akashlevy/ember-pcb/ember-pcb.kicad_sch

## KiCad design ember-pcb.kicad_sch (2023-03-14)

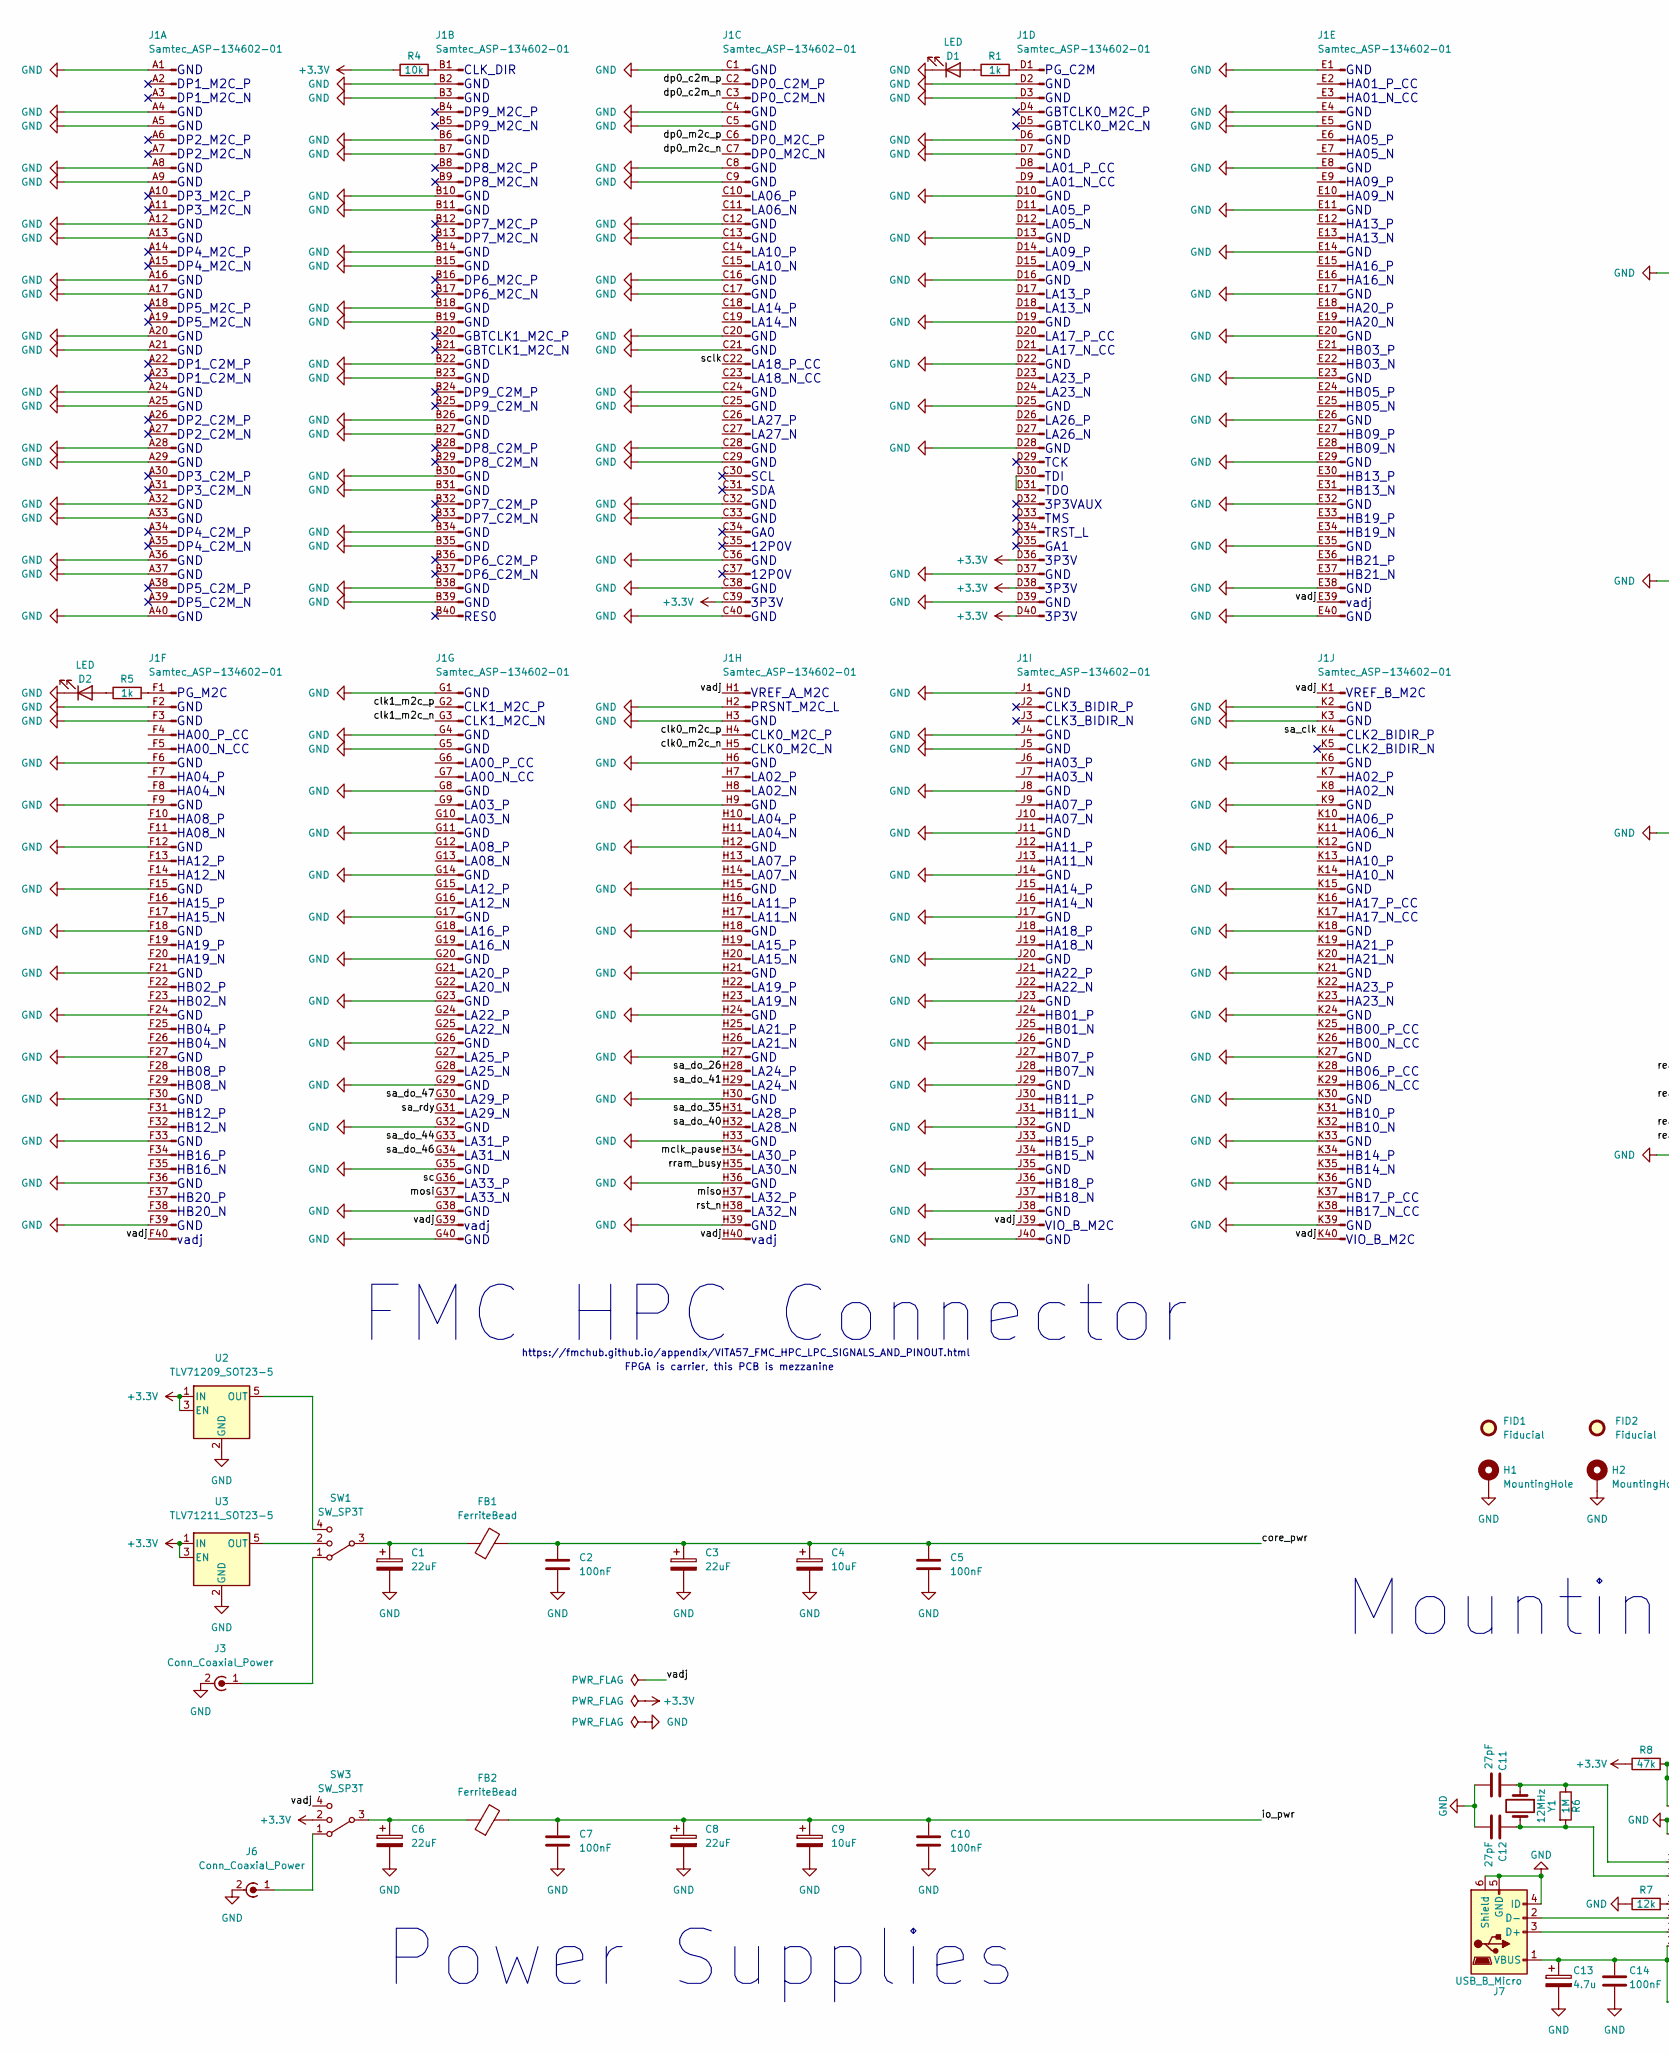
[picture p3: schematic ember-pcb.kicad_sch, part in row 1, column 1]

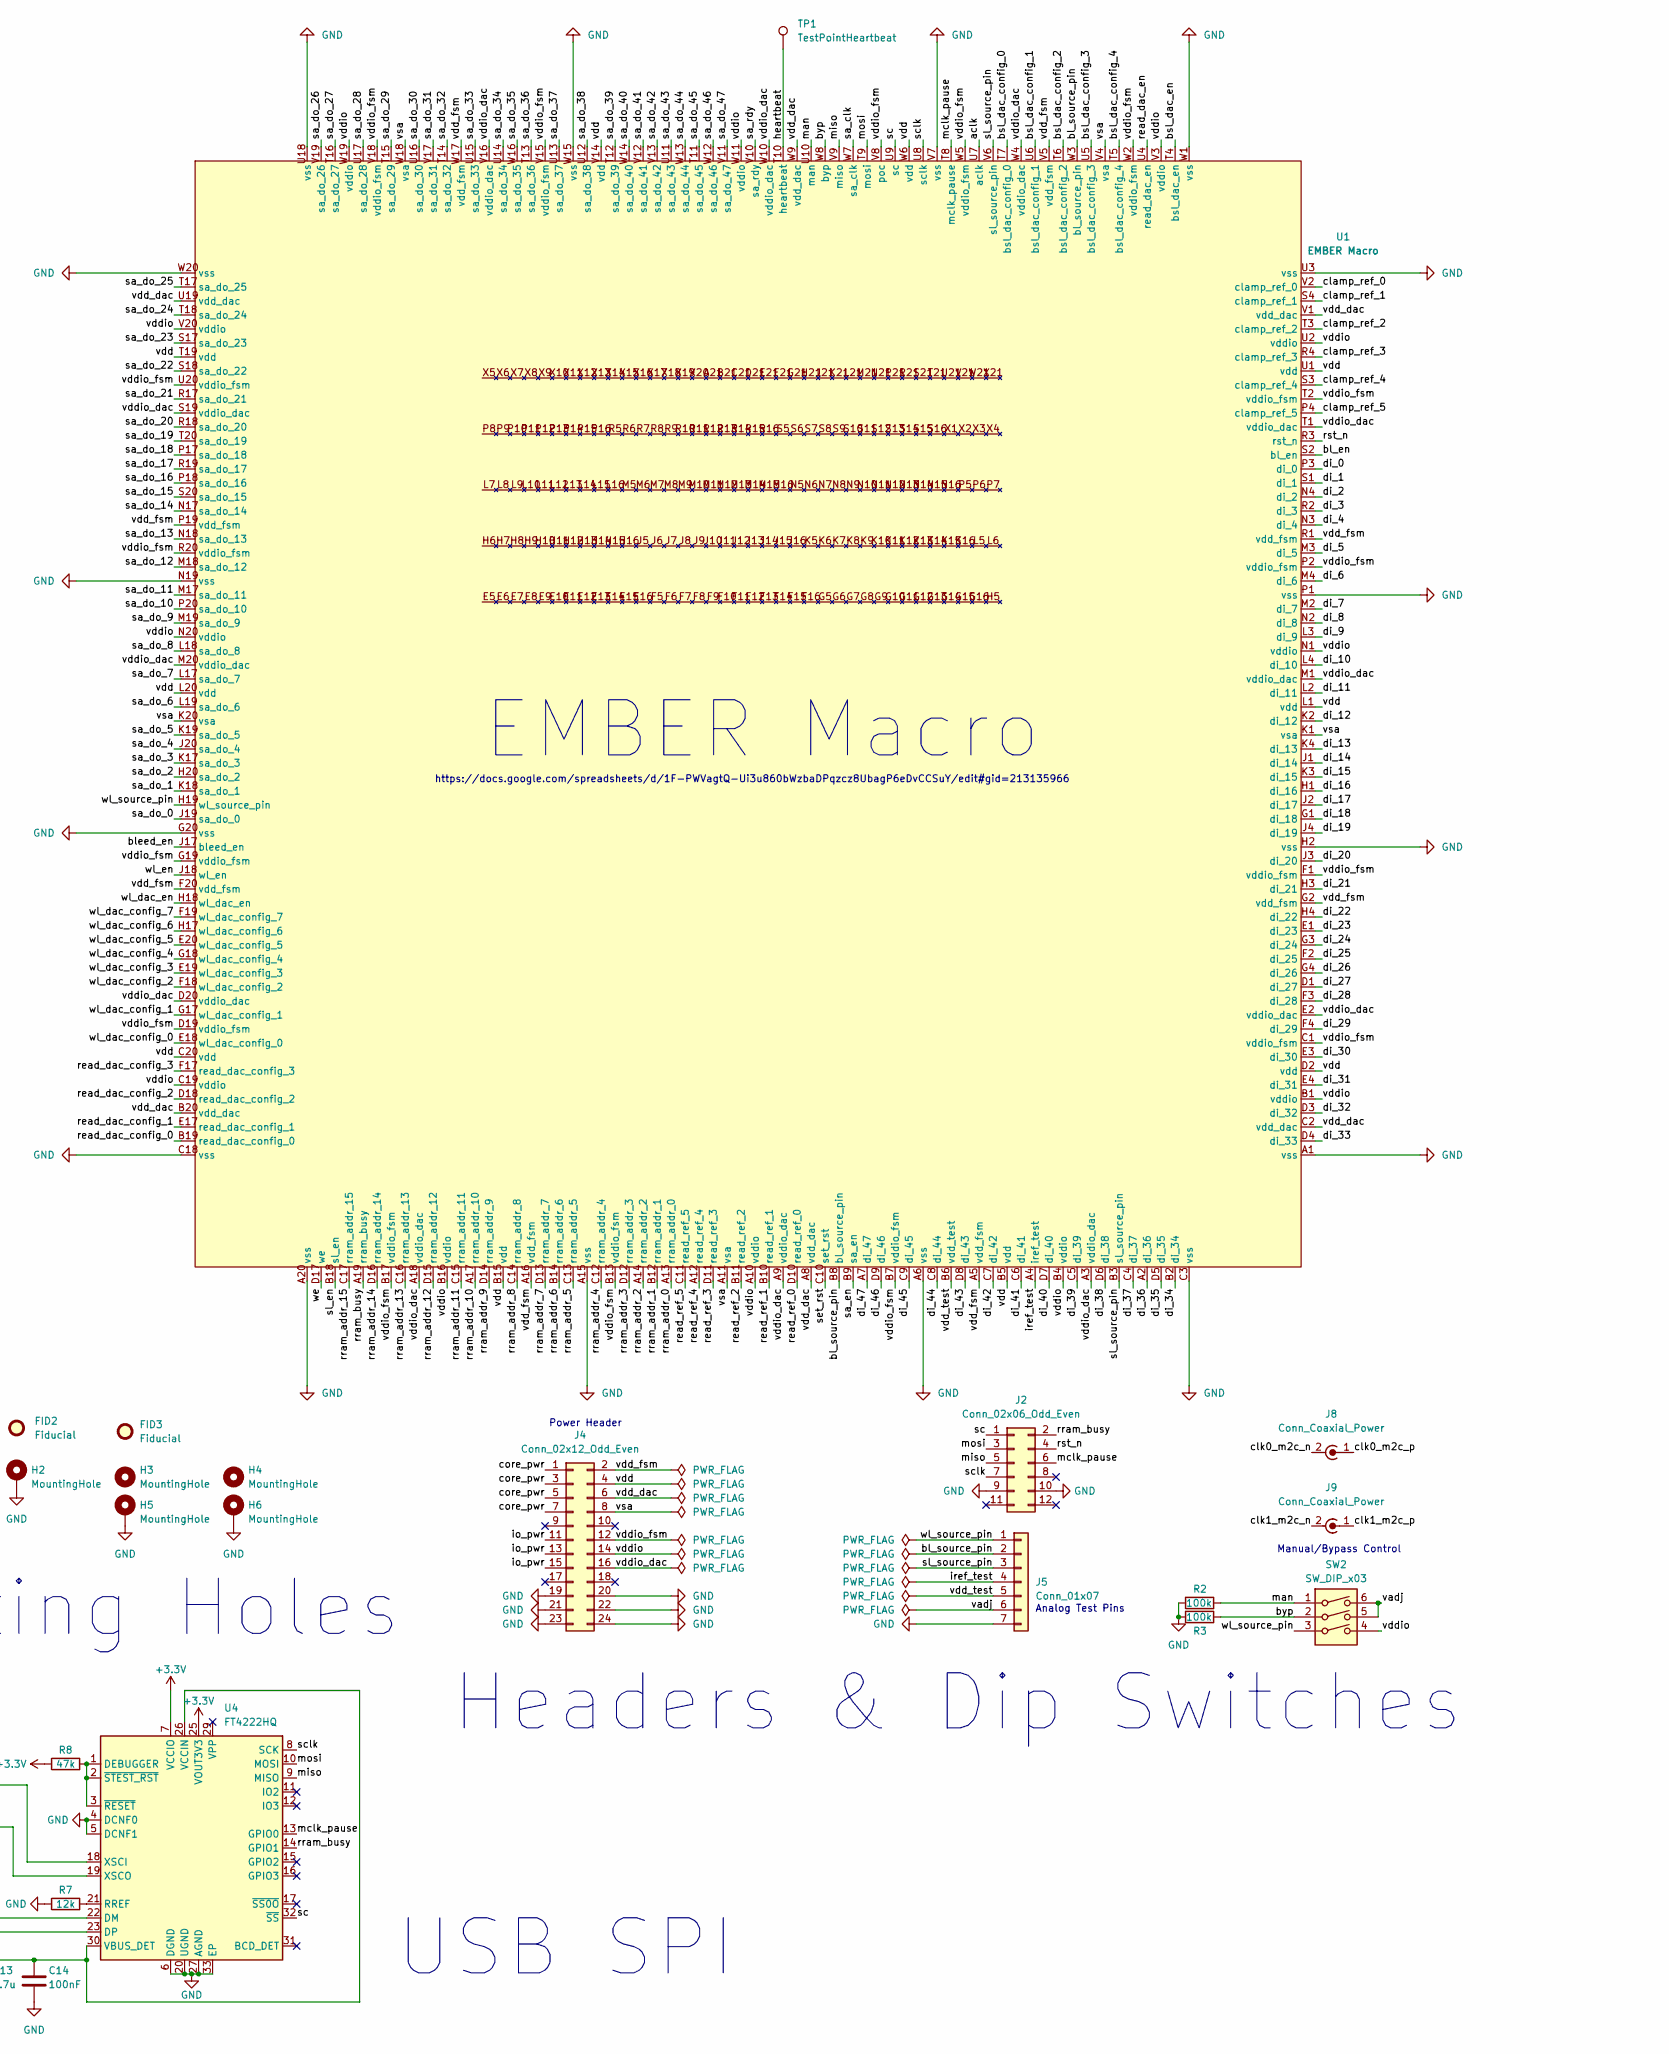
[picture p4: schematic ember-pcb.kicad_sch, part in row 1, column 2]

Parts:
C1, C3, C6, C8: 22uF; CP_EIA-3528-21_Kemet-B
C2, C5, C7, C10, C14: 100nF; C_1210_3225Metric
C4, C9: 10uF; CP_EIA-3528-12_Kemet-T
C11, C12: 27pF; C_0603_1608Metric
C13: 4.7u; CP_EIA-3528-12_Kemet-T
D1, D2: LED; LED_0603_1608Metric
FB1, FB2: FerriteBead; LairdTech_28C0236-0JW-10
FID1, FID2, FID3: Fiducial; Fiducial_1mm_Mask3mm
H1, H2: MountingHole; MountingHole_2.5mm_Pad
H3, H4: MountingHole; MountingHole_2.5mm
H5, H6: MountingHole; MountingHole_3mm_Pad
J1: Samtec_ASP-134602-01; Samtec_FMC_ASP-134602-01_10x40_P1.27mm_Vertical
J2: Conn_02x06_Odd_Even; PinHeader_2x06_P2.54mm_Vertical
J3, J6, J8, J9: Conn_Coaxial_Power; SMA_Molex_73251-2200_Horizontal
J4: Conn_02x12_Odd_Even; PinHeader_2x12_P2.54mm_Vertical
J5: Conn_01x07; PinHeader_1x07_P2.54mm_Vertical
J7: USB_B_Micro; USB_Micro-B_Molex-105017-0001
R1, R5: 1k; R_0603_1608Metric
R2, R3: 100k; R_0603_1608Metric
R4: 10k; R_0603_1608Metric
R6: 1M; R_0603_1608Metric
R7: 12k; R_0603_1608Metric
R8: 47k; R_0603_1608Metric
SW1, SW3: SW_SP3T; SW_SP3T_PCM13
SW2: SW_DIP_x03; SW_DIP_SPSTx03_Slide_Omron_A6S-310x_W8.9mm_P2.54mm
TP1: TestPointHeartbeat; TestPoint_Pad_D1.0mm
U1: EMBER Macro; ARIES_441-PRS21001-12
U2: TLV71209_SOT23-5; SOT-23-5
U3: TLV71211_SOT23-5; SOT-23-5
U4: FT4222HQ; VQFN-32-1EP_5x5mm_P0.5mm_EP3.1x3.1mm
Y1: 12MHz; Crystal_SMD_0603-2Pin_6.0x3.5mm

Connections:
+3.3V: J1.C39 (Pin_39), J1.D36 (Pin_36), J1.D38 (Pin_38), J1.D40 (Pin_40), R4.1, R8.1, SW3.2, U2.1 (IN), U2.3 (EN), U3.1 (IN), U3.3 (EN), U4.7 (VCCIO), U4.25 (VOUT3V3)
GND: C1.2, C2.2, C3.2, C4.2, C5.2, C6.2, C7.2, C8.2, C9.2, C10.2, C11.2, C12.2, C13.2, C14.2, D1.1 (K), D2.1 (K), H1.1, H2.1, H5.1, H6.1, J1.A1 (Pin_1), J1.A4 (Pin_4), J1.A5 (Pin_5), J1.A8 (Pin_8), J1.A9 (Pin_9), J1.A12 (Pin_12), J1.A13 (Pin_13), J1.A16 (Pin_16), J1.A17 (Pin_17), J1.A20 (Pin_20), J1.A21 (Pin_21), J1.A24 (Pin_24), J1.A25 (Pin_25), J1.A28 (Pin_28), J1.A29 (Pin_29), J1.A32 (Pin_32), J1.A33 (Pin_33), J1.A36 (Pin_36), J1.A37 (Pin_37), J1.A40 (Pin_40), J1.B2 (Pin_2), J1.B3 (Pin_3), J1.B6 (Pin_6), J1.B7 (Pin_7), J1.B10 (Pin_10), J1.B11 (Pin_11), J1.B14 (Pin_14), J1.B15 (Pin_15), J1.B18 (Pin_18), J1.B19 (Pin_19), J1.B22 (Pin_22), J1.B23 (Pin_23), J1.B26 (Pin_26), J1.B27 (Pin_27), J1.B30 (Pin_30), J1.B31 (Pin_31), J1.B34 (Pin_34), J1.B35 (Pin_35), J1.B38 (Pin_38), J1.B39 (Pin_39), J1.C1 (Pin_1), J1.C4 (Pin_4), J1.C5 (Pin_5), J1.C8 (Pin_8), J1.C9 (Pin_9), J1.C12 (Pin_12), J1.C13 (Pin_13), J1.C16 (Pin_16), J1.C17 (Pin_17), J1.C20 (Pin_20), J1.C21 (Pin_21), J1.C24 (Pin_24), J1.C25 (Pin_25), J1.C28 (Pin_28), J1.C29 (Pin_29), J1.C32 (Pin_32), J1.C33 (Pin_33), J1.C36 (Pin_36), J1.C38 (Pin_38), J1.C40 (Pin_40), J1.D2 (Pin_2), J1.D3 (Pin_3), J1.D6 (Pin_6), J1.D7 (Pin_7), J1.D10 (Pin_10), J1.D13 (Pin_13), J1.D16 (Pin_16), J1.D19 (Pin_19), J1.D22 (Pin_22), J1.D25 (Pin_25), J1.D28 (Pin_28), J1.D37 (Pin_37), J1.D39 (Pin_39), J1.E1 (Pin_1), J1.E4 (Pin_4), J1.E5 (Pin_5), J1.E8 (Pin_8), J1.E11 (Pin_11), J1.E14 (Pin_14), J1.E17 (Pin_17), J1.E20 (Pin_20), J1.E23 (Pin_23), J1.E26 (Pin_26), J1.E29 (Pin_29), J1.E32 (Pin_32), J1.E35 (Pin_35), J1.E38 (Pin_38), J1.E40 (Pin_40), J1.F2 (Pin_2), J1.F3 (Pin_3), J1.F6 (Pin_6), J1.F9 (Pin_9), J1.F12 (Pin_12), J1.F15 (Pin_15), J1.F18 (Pin_18), J1.F21 (Pin_21), J1.F24 (Pin_24), J1.F27 (Pin_27), J1.F30 (Pin_30), J1.F33 (Pin_33), J1.F36 (Pin_36), J1.F39 (Pin_39), J1.G1 (Pin_1), J1.G4 (Pin_4), J1.G5 (Pin_5), J1.G8 (Pin_8), J1.G11 (Pin_11), J1.G14 (Pin_14), J1.G17 (Pin_17), J1.G20 (Pin_20), J1.G23 (Pin_23), J1.G26 (Pin_26), J1.G29 (Pin_29), J1.G32 (Pin_32), J1.G35 (Pin_35), J1.G38 (Pin_38), J1.G40 (Pin_40), J1.H2 (Pin_2), J1.H3 (Pin_3), J1.H6 (Pin_6), J1.H9 (Pin_9), J1.H12 (Pin_12), J1.H15 (Pin_15), J1.H18 (Pin_18), J1.H21 (Pin_21), J1.H24 (Pin_24), J1.H27 (Pin_27), J1.H30 (Pin_30), J1.H33 (Pin_33), J1.H36 (Pin_36), J1.H39 (Pin_39), J1.J1 (Pin_1), J1.J4 (Pin_4), J1.J5 (Pin_5), J1.J8 (Pin_8), J1.J11 (Pin_11), J1.J14 (Pin_14), J1.J17 (Pin_17), J1.J20 (Pin_20), J1.J23 (Pin_23), J1.J26 (Pin_26), J1.J29 (Pin_29), J1.J32 (Pin_32), J1.J35 (Pin_35), J1.J38 (Pin_38), J1.J40 (Pin_40), J1.K2 (Pin_2), J1.K3 (Pin_3), J1.K6 (Pin_6), J1.K9 (Pin_9), J1.K12 (Pin_12), J1.K15 (Pin_15), J1.K18 (Pin_18), J1.K21 (Pin_21), J1.K24 (Pin_24), J1.K27 (Pin_27), J1.K30 (Pin_30), J1.K33 (Pin_33), J1.K36 (Pin_36), J1.K39 (Pin_39), J2.9, J2.10, J3.2 (Ext), J4.19, J4.20, J4.21, J4.22, J4.23, J4.24, J5.7, J6.2 (Ext), J7.4 (ID), J7.5 (GND), J7.6 (Shield), R2.2, R3.2, R7.1, U1.A1 (vss), U1.A6 (vss), U1.A15 (vss), U1.A20 (vss), U1.C3 (vss), U1.C18 (vss), U1.G20 (vss), U1.H2 (vss), U1.N19 (vss), U1.P1 (vss), U1.U3 (vss), U1.U18 (vss), U1.V7 (vss), U1.W1 (vss), U1.W15 (vss), U1.W20 (vss), U2.2 (GND), U3.2 (GND), U4.4 (DCNF0), U4.5 (DCNF1), U4.6 (DGND), U4.20 (UGND), U4.24 (UGND), U4.27 (AGND), U4.28 (DGND), U4.33 (EP)
unnamed: C1.1, FB1.1, SW1.3
unnamed: C6.1, FB2.1, SW3.3
unnamed: C11.1, R6.1, U4.18 (XSCI), Y1.1
unnamed: C12.1, R6.2, U4.19 (XSCO), Y1.2
unnamed: C13.1, C14.1, J7.1 (VBUS), U4.26 (VCCIN), U4.30 (VBUS_DET)
unnamed: D1.2 (A), R1.1
unnamed: D2.2 (A), R5.1
unnamed: J1.B1 (Pin_1), R4.2
unnamed: J1.D1 (Pin_1), R1.2
unnamed: J1.D30 (Pin_30), J1.D31 (Pin_31)
unnamed: J1.F1 (Pin_1), R5.2
unnamed: J3.1 (In), SW1.1
unnamed: J6.1 (In), SW3.1
unnamed: J7.2 (D-), U4.22 (DM)
unnamed: J7.3 (D+), U4.23 (DP)
unnamed: R7.2, U4.21 (RREF)
unnamed: R8.2, U4.1 (DEBUGGER), U4.2 (~STEST_RST), U4.3 (~RESET)
unnamed: SW1.2, U3.5 (OUT)
unnamed: SW1.4, U2.5 (OUT)
aclk: U1.U7 (aclk)
bl_en: U1.S2 (bl_en)
bl_source_pin: J5.2, U1.B8 (bl_source_pin), U1.W3 (bl_source_pin)
bleed_en: U1.J17 (bleed_en)
bsl_dac_config_0: U1.T7 (bsl_dac_config_0)
bsl_dac_config_1: U1.U6 (bsl_dac_config_1)
bsl_dac_config_2: U1.T6 (bsl_dac_config_2)
bsl_dac_config_3: U1.U5 (bsl_dac_config_3)
bsl_dac_config_4: U1.T5 (bsl_dac_config_4)
bsl_dac_en: U1.T4 (bsl_dac_en)
byp: R3.1, SW2.2, U1.W8 (byp)
clamp_ref_0: U1.V2 (clamp_ref_0)
clamp_ref_1: U1.S4 (clamp_ref_1)
clamp_ref_2: U1.T3 (clamp_ref_2)
clamp_ref_3: U1.R4 (clamp_ref_3)
clamp_ref_4: U1.S3 (clamp_ref_4)
clamp_ref_5: U1.P4 (clamp_ref_5)
clk0_m2c_n: J1.H5 (Pin_5), J8.2 (Ext)
clk0_m2c_p: J1.H4 (Pin_4), J8.1 (In)
clk1_m2c_n: J1.G3 (Pin_3), J9.2 (Ext)
clk1_m2c_p: J1.G2 (Pin_2), J9.1 (In)
core_pwr: C2.1, C3.1, C4.1, C5.1, FB1.2, J4.1, J4.3, J4.5, J4.7
di_0: U1.P3 (di_0)
di_1: U1.S1 (di_1)
di_2: U1.N4 (di_2)
di_3: U1.R2 (di_3)
di_4: U1.N3 (di_4)
di_5: U1.M3 (di_5)
di_6: U1.M4 (di_6)
di_7: U1.M2 (di_7)
di_8: U1.N2 (di_8)
di_9: U1.L3 (di_9)
di_10: U1.L4 (di_10)
di_11: U1.L2 (di_11)
di_12: U1.K2 (di_12)
di_13: U1.K4 (di_13)
di_14: U1.J1 (di_14)
di_15: U1.K3 (di_15)
di_16: U1.H1 (di_16)
di_17: U1.J2 (di_17)
di_18: U1.G1 (di_18)
di_19: U1.J4 (di_19)
di_20: U1.J3 (di_20)
di_21: U1.H3 (di_21)
di_22: U1.H4 (di_22)
di_23: U1.E1 (di_23)
di_24: U1.G3 (di_24)
di_25: U1.F2 (di_25)
di_26: U1.G4 (di_26)
di_27: U1.D1 (di_27)
di_28: U1.F3 (di_28)
di_29: U1.F4 (di_29)
di_30: U1.E3 (di_30)
di_31: U1.E4 (di_31)
di_32: U1.D3 (di_32)
di_33: U1.D4 (di_33)
di_34: U1.B2 (di_34)
di_35: U1.D5 (di_35)
di_36: U1.A2 (di_36)
di_37: U1.C4 (di_37)
di_38: U1.D6 (di_38)
di_39: U1.C5 (di_39)
di_40: U1.D7 (di_40)
di_41: U1.C6 (di_41)
di_42: U1.C7 (di_42)
di_43: U1.D8 (di_43)
di_44: U1.C8 (di_44)
di_45: U1.C9 (di_45)
di_46: U1.D9 (di_46)
di_47: U1.A7 (di_47)
dp0_c2m_n: J1.C3 (Pin_3)
dp0_c2m_p: J1.C2 (Pin_2)
dp0_m2c_n: J1.C7 (Pin_7)
dp0_m2c_p: J1.C6 (Pin_6)
heartbeat: TP1.1, U1.T10 (heartbeat)
io_pwr: C7.1, C8.1, C9.1, C10.1, FB2.2, J4.11, J4.13, J4.15
iref_test: J5.4, U1.A4 (iref_test)
man: R2.1, SW2.1, U1.U10 (man)
mclk_pause: J1.H34 (Pin_34), J2.6, U1.T8 (mclk_pause), U4.13 (GPIO0)
miso: J1.H37 (Pin_37), J2.5, U1.V9 (miso), U4.9 (MISO)
mosi: J1.G37 (Pin_37), J2.3, U1.T9 (mosi), U4.10 (MOSI)
read_dac_config_0: U1.B19 (read_dac_config_0)
read_dac_config_1: U1.E17 (read_dac_config_1)
read_dac_config_2: U1.D18 (read_dac_config_2)
read_dac_config_3: U1.F17 (read_dac_config_3)
read_dac_en: U1.U4 (read_dac_en)
read_ref_0: U1.D10 (read_ref_0)
read_ref_1: U1.B10 (read_ref_1)
read_ref_2: U1.B11 (read_ref_2)
read_ref_3: U1.D11 (read_ref_3)
read_ref_4: U1.A12 (read_ref_4)
read_ref_5: U1.C11 (read_ref_5)
rram_addr_0: U1.A13 (rram_addr_0)
rram_addr_1: U1.B12 (rram_addr_1)
rram_addr_2: U1.A14 (rram_addr_2)
rram_addr_3: U1.D12 (rram_addr_3)
rram_addr_4: U1.C12 (rram_addr_4)
rram_addr_5: U1.C13 (rram_addr_5)
rram_addr_6: U1.B14 (rram_addr_6)
rram_addr_7: U1.D13 (rram_addr_7)
rram_addr_8: U1.C14 (rram_addr_8)
rram_addr_9: U1.D14 (rram_addr_9)
rram_addr_10: U1.A17 (rram_addr_10)
rram_addr_11: U1.C15 (rram_addr_11)
rram_addr_12: U1.D15 (rram_addr_12)
rram_addr_13: U1.C16 (rram_addr_13)
rram_addr_14: U1.D16 (rram_addr_14)
rram_addr_15: U1.C17 (rram_addr_15)
rram_busy: J1.H35 (Pin_35), J2.2, U1.A19 (rram_busy), U4.14 (GPIO1)
rst_n: J1.H38 (Pin_38), J2.4, U1.R3 (rst_n)
sa_clk: J1.K4 (Pin_4), U1.W7 (sa_clk)
sa_do_0: U1.J19 (sa_do_0)
sa_do_1: U1.K18 (sa_do_1)
sa_do_2: U1.H20 (sa_do_2)
sa_do_3: U1.K17 (sa_do_3)
sa_do_4: U1.J20 (sa_do_4)
sa_do_5: U1.K19 (sa_do_5)
sa_do_6: U1.L19 (sa_do_6)
sa_do_7: U1.L17 (sa_do_7)
sa_do_8: U1.L18 (sa_do_8)
sa_do_9: U1.M19 (sa_do_9)
sa_do_10: U1.P20 (sa_do_10)
sa_do_11: U1.M17 (sa_do_11)
sa_do_12: U1.M18 (sa_do_12)
sa_do_13: U1.N18 (sa_do_13)
sa_do_14: U1.N17 (sa_do_14)
sa_do_15: U1.S20 (sa_do_15)
sa_do_16: U1.P18 (sa_do_16)
sa_do_17: U1.R19 (sa_do_17)
sa_do_18: U1.P17 (sa_do_18)
sa_do_19: U1.T20 (sa_do_19)
sa_do_20: U1.R18 (sa_do_20)
sa_do_21: U1.R17 (sa_do_21)
sa_do_22: U1.S18 (sa_do_22)
sa_do_23: U1.S17 (sa_do_23)
sa_do_24: U1.T18 (sa_do_24)
sa_do_25: U1.T17 (sa_do_25)
sa_do_26: J1.H28 (Pin_28), U1.V19 (sa_do_26)
sa_do_27: U1.T16 (sa_do_27)
sa_do_28: U1.U17 (sa_do_28)
sa_do_29: U1.T15 (sa_do_29)
sa_do_30: U1.U16 (sa_do_30)
sa_do_31: U1.V17 (sa_do_31)
sa_do_32: U1.T14 (sa_do_32)
sa_do_33: U1.U15 (sa_do_33)
sa_do_34: U1.U14 (sa_do_34)
sa_do_35: J1.H31 (Pin_31), U1.W16 (sa_do_35)
sa_do_36: U1.T13 (sa_do_36)
sa_do_37: U1.U13 (sa_do_37)
sa_do_38: U1.U12 (sa_do_38)
sa_do_39: U1.T12 (sa_do_39)
sa_do_40: J1.H32 (Pin_32), U1.W14 (sa_do_40)
sa_do_41: J1.H29 (Pin_29), U1.V12 (sa_do_41)
sa_do_42: U1.V13 (sa_do_42)
sa_do_43: U1.U11 (sa_do_43)
sa_do_44: J1.G33 (Pin_33), U1.W13 (sa_do_44)
sa_do_45: U1.T11 (sa_do_45)
sa_do_46: J1.G34 (Pin_34), U1.W12 (sa_do_46)
sa_do_47: J1.G30 (Pin_30), U1.V11 (sa_do_47)
sa_en: U1.B9 (sa_en)
sa_rdy: J1.G31 (Pin_31), U1.V10 (sa_rdy)
sc: J1.G36 (Pin_36), J2.1, U1.U9 (sc), U4.32 (~SS)
sclk: J1.C22 (Pin_22), J2.7, U1.U8 (sclk), U4.8 (SCK)
set_rst: U1.C10 (set_rst)
sl_en: U1.B18 (sl_en)
sl_source_pin: J5.3, U1.B3 (sl_source_pin), U1.V6 (sl_source_pin)
vadj: J1.E39 (Pin_39), J1.F40 (Pin_40), J1.G39 (Pin_39), J1.H1 (Pin_1), J1.H40 (Pin_40), J1.J39 (Pin_39), J1.K1 (Pin_1), J1.K40 (Pin_40), J5.6, SW2.5, SW2.6, SW3.4
vdd: J4.4, U1.B5 (vdd), U1.B15 (vdd), U1.C20 (vdd), U1.D2 (vdd), U1.L1 (vdd), U1.L20 (vdd), U1.T19 (vdd), U1.U1 (vdd), U1.V14 (vdd), U1.W6 (vdd)
vdd_dac: J4.6, U1.A8 (vdd_dac), U1.B20 (vdd_dac), U1.C2 (vdd_dac), U1.U19 (vdd_dac), U1.V1 (vdd_dac), U1.W9 (vdd_dac)
vdd_fsm: J4.2, U1.A5 (vdd_fsm), U1.A16 (vdd_fsm), U1.F20 (vdd_fsm), U1.G2 (vdd_fsm), U1.P19 (vdd_fsm), U1.R1 (vdd_fsm), U1.V5 (vdd_fsm), U1.W17 (vdd_fsm)
vdd_test: J5.5, U1.B6 (vdd_test)
vddio: J4.14, SW2.4, U1.A10 (vddio), U1.B1 (vddio), U1.B4 (vddio), U1.B16 (vddio), U1.C19 (vddio), U1.N1 (vddio), U1.N20 (vddio), U1.U2 (vddio), U1.V3 (vddio), U1.V20 (vddio), U1.W11 (vddio), U1.W19 (vddio)
vddio_dac: J4.16, U1.A3 (vddio_dac), U1.A9 (vddio_dac), U1.A18 (vddio_dac), U1.D20 (vddio_dac), U1.E2 (vddio_dac), U1.M1 (vddio_dac), U1.M20 (vddio_dac), U1.S19 (vddio_dac), U1.T1 (vddio_dac), U1.V16 (vddio_dac), U1.W4 (vddio_dac), U1.W10 (vddio_dac)
vddio_fsm: J4.12, U1.B7 (vddio_fsm), U1.B13 (vddio_fsm), U1.B17 (vddio_fsm), U1.C1 (vddio_fsm), U1.D19 (vddio_fsm), U1.F1 (vddio_fsm), U1.G19 (vddio_fsm), U1.P2 (vddio_fsm), U1.R20 (vddio_fsm), U1.T2 (vddio_fsm), U1.U20 (vddio_fsm), U1.V8 (poc), U1.V15 (vddio_fsm), U1.V18 (vddio_fsm), U1.W2 (vddio_fsm), U1.W5 (vddio_fsm)
vsa: J4.8, U1.A11 (vsa), U1.K1 (vsa), U1.K20 (vsa), U1.V4 (vsa), U1.W18 (vsa)
we: U1.D17 (we)
wl_dac_config_0: U1.E18 (wl_dac_config_0)
wl_dac_config_1: U1.G17 (wl_dac_config_1)
wl_dac_config_2: U1.F18 (wl_dac_config_2)
wl_dac_config_3: U1.E19 (wl_dac_config_3)
wl_dac_config_4: U1.G18 (wl_dac_config_4)
wl_dac_config_5: U1.E20 (wl_dac_config_5)
wl_dac_config_6: U1.H17 (wl_dac_config_6)
wl_dac_config_7: U1.F19 (wl_dac_config_7)
wl_dac_en: U1.H18 (wl_dac_en)
wl_en: U1.J18 (wl_en)
wl_source_pin: J5.1, SW2.3, U1.H19 (wl_source_pin)

Notes on the sheet:
Manual/Bypass Control
VREF_B_M2C GND GND CLK2_BIDIR_P CLK2_BIDIR_N GND HA02_P HA02_N GND HA06_P HA06_N GND HA10_P HA10_N GND HA17_P_CC HA17_N_CC GND HA21_P HA21_N GND HA23_P HA23_N GND HB00_P_CC HB00_N_CC GND HB06_P_CC HB06_N_CC GND HB10_P HB10_N GND HB14_P HB14_N GND HB17_P_CC HB17_N_CC GND VIO_B_M2C
https://fmchub.github.io/appendix/VITA57_FMC_HPC_LPC_SIGNALS_AND_PINOUT.html
GND DP1_M2C_P DP1_M2C_N GND GND DP2_M2C_P DP2_M2C_N GND GND DP3_M2C_P DP3_M2C_N GND GND DP4_M2C_P DP4_M2C_N GND GND DP5_M2C_P DP5_M2C_N GND GND DP1_C2M_P DP1_C2M_N GND GND DP2_C2M_P DP2_C2M_N GND GND DP3_C2M_P DP3_C2M_N GND GND DP4_C2M_P DP4_C2M_N GND GND DP5_C2M_P DP5_C2M_N GND
USB SPI
VREF_A_M2C PRSNT_M2C_L GND CLK0_M2C_P CLK0_M2C_N GND LA02_P LA02_N GND LA04_P LA04_N GND LA07_P LA07_N GND LA11_P LA11_N GND LA15_P LA15_N GND LA19_P LA19_N GND LA21_P LA21_N GND LA24_P LA24_N GND LA28_P LA28_N GND LA30_P LA30_N GND LA32_P LA32_N GND vadj
PG_M2C GND GND HA00_P_CC HA00_N_CC GND HA04_P HA04_N GND HA08_P HA08_N GND HA12_P HA12_N GND HA15_P HA15_N GND HA19_P HA19_N GND HB02_P HB02_N GND HB04_P HB04_N GND HB08_P HB08_N GND HB12_P HB12_N GND HB16_P HB16_N GND HB20_P HB20_N GND vadj
https://docs.google.com/spreadsheets/d/1F-PWVagtQ-Ui3u860bWzbaDPqzcz8UbagP6eDvCCSuY/edit#gid=213135966
GND CLK3_BIDIR_P CLK3_BIDIR_N GND GND HA03_P HA03_N GND HA07_P HA07_N GND HA11_P HA11_N GND HA14_P HA14_N GND HA18_P HA18_N GND HA22_P HA22_N GND HB01_P HB01_N GND HB07_P HB07_N GND HB11_P HB11_N GND HB15_P HB15_N GND HB18_P HB18_N GND VIO_B_M2C GND
FMC HPC Connector
EMBER Macro
Mounting Holes
Power Supplies
Analog Test Pins
GND CLK1_M2C_P CLK1_M2C_N GND GND LA00_P_CC LA00_N_CC GND LA03_P LA03_N GND LA08_P LA08_N GND LA12_P LA12_N GND LA16_P LA16_N GND LA20_P LA20_N GND LA22_P LA22_N GND LA25_P LA25_N GND LA29_P LA29_N GND LA31_P LA31_N GND LA33_P LA33_N GND vadj GND
FPGA is carrier, this PCB is mezzanine
GND HA01_P_CC HA01_N_CC GND GND HA05_P HA05_N GND HA09_P HA09_N GND HA13_P HA13_N GND HA16_P HA16_N GND HA20_P HA20_N GND HB03_P HB03_N GND HB05_P HB05_N GND HB09_P HB09_N GND HB13_P HB13_N GND HB19_P HB19_N GND HB21_P HB21_N GND vadj GND
Power Header
PG_C2M GND GND GBTCLK0_M2C_P GBTCLK0_M2C_N GND GND LA01_P_CC LA01_N_CC GND LA05_P LA05_N GND LA09_P LA09_N GND LA13_P LA13_N GND LA17_P_CC LA17_N_CC GND LA23_P LA23_N GND LA26_P LA26_N GND TCK TDI TDO 3P3VAUX TMS TRST_L GA1 3P3V GND 3P3V GND 3P3V
CLK_DIR GND GND DP9_M2C_P DP9_M2C_N GND GND DP8_M2C_P DP8_M2C_N GND GND DP7_M2C_P DP7_M2C_N GND GND DP6_M2C_P DP6_M2C_N GND GND GBTCLK1_M2C_P GBTCLK1_M2C_N GND GND DP9_C2M_P DP9_C2M_N GND GND DP8_C2M_P DP8_C2M_N GND GND DP7_C2M_P DP7_C2M_N GND GND DP6_C2M_P DP6_C2M_N GND GND RES0
Headers & Dip Switches
GND DP0_C2M_P DP0_C2M_N GND GND DP0_M2C_P DP0_M2C_N GND GND LA06_P LA06_N GND GND LA10_P LA10_N GND GND LA14_P LA14_N GND GND LA18_P_CC LA18_N_CC GND GND LA27_P LA27_N GND GND SCL SDA GND GND GA0 12P0V GND 12P0V GND 3P3V GND
